NStevenU/WaveCanvas/include/logo_data.h

#pragma once
#include <Arduino.h>

// Icon: logo (logo.gif, 3143 bytes)
const size_t ICON_LOGO_GIF_SIZE = 3143;
const uint8_t ICON_LOGO_GIF_DATA[] PROGMEM = {
0x47, 0x49, 0x46, 0x38, 0x39, 0x61, 0xb6, 0x00, 0x2a, 0x00, 0x87, 0x00, 0x00, 0xf0, 0xf0, 0xf0, 
0xef, 0xef, 0xef, 0xee, 0xee, 0xee, 0xed, 0xed, 0xed, 0xec, 0xec, 0xec, 0xeb, 0xeb, 0xeb, 0xea, 
0xea, 0xea, 0xe9, 0xe9, 0xe9, 0xe8, 0xe8, 0xe8, 0xe7, 0xe7, 0xe7, 0xe6, 0xe6, 0xe6, 0xe5, 0xe5, 
0xe5, 0xe4, 0xe4, 0xe4, 0xe3, 0xe3, 0xe3, 0xe2, 0xe2, 0xe2, 0xe1, 0xe1, 0xe1, 0xe0, 0xe0, 0xe0, 
0xdf, 0xdf, 0xdf, 0xde, 0xde, 0xde, 0xdc, 0xdc, 0xdc, 0xdb, 0xdb, 0xdb, 0xda, 0xda, 0xda, 0xd9, 
0xd9, 0xd9, 0xd8, 0xd8, 0xd8, 0xd7, 0xd7, 0xd7, 0xd6, 0xd6, 0xd6, 0xd5, 0xd5, 0xd5, 0xd4, 0xd4, 
0xd4, 0xd3, 0xd3, 0xd3, 0xd2, 0xd2, 0xd2, 0xd1, 0xd1, 0xd1, 0xd0, 0xd0, 0xd0, 0xcf, 0xcf, 0xcf, 
0xce, 0xce, 0xce, 0xcd, 0xcd, 0xcd, 0xcc, 0xcc, 0xcc, 0xcb, 0xcb, 0xcb, 0xca, 0xca, 0xca, 0xc8, 
0xc8, 0xc8, 0xc7, 0xc7, 0xc7, 0xc6, 0xc6, 0xc6, 0xc4, 0xc4, 0xc4, 0xc3, 0xc3, 0xc3, 0xc2, 0xc2, 
0xc2, 0xc1, 0xc1, 0xc1, 0xc0, 0xc0, 0xc0, 0xbf, 0xbf, 0xbf, 0xbe, 0xbe, 0xbe, 0xbc, 0xbc, 0xbc, 
0xbb, 0xbb, 0xbb, 0xb9, 0xb9, 0xb9, 0xb8, 0xb8, 0xb8, 0xb7, 0xb7, 0xb7, 0xb6, 0xb6, 0xb6, 0xb5, 
0xb5, 0xb5, 0xb4, 0xb4, 0xb4, 0xb3, 0xb3, 0xb3, 0xb2, 0xb2, 0xb2, 0xb1, 0xb1, 0xb1, 0xb0, 0xb0, 
0xb0, 0xaf, 0xaf, 0xaf, 0xad, 0xad, 0xad, 0xac, 0xac, 0xac, 0xab, 0xab, 0xab, 0xaa, 0xaa, 0xaa, 
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
0x25, 0x25, 0x25, 0x24, 0x24, 0x24, 0x23, 0x23, 0x23, 0x22, 0x22, 0x22, 0x21, 0x21, 0x21, 0x20, 
0x20, 0x20, 0x1f, 0x1f, 0x1f, 0x1e, 0x1e, 0x1e, 0x1d, 0x1d, 0x1d, 0x1c, 0x1c, 0x1c, 0x1b, 0x1b, 
0x1b, 0x1a, 0x1a, 0x1a, 0x19, 0x19, 0x19, 0x18, 0x18, 0x18, 0x17, 0x17, 0x17, 0x16, 0x16, 0x16, 
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
};
