NStevenU/WaveCanvas/include/icon_data.h

#pragma once
#include <Arduino.h>

// Icon: music (music.gif, 136 bytes)
const size_t ICON_MUSIC_GIF_SIZE = 136;
const uint8_t ICON_MUSIC_GIF_DATA[] PROGMEM = {
0x47, 0x49, 0x46, 0x38, 0x39, 0x61, 0x10, 0x00, 0x10, 0x00, 0x82, 0x00, 0x00, 0xcc, 0xcc, 0xcc, 
0x99, 0x99, 0x99, 0x66, 0x66, 0x66, 0x33, 0x33, 0x33, 0x00, 0x00, 0x00, 0x00, 0x00, 0x00, 0x00, 
0x00, 0x00, 0x00, 0x00, 0x00, 0x21, 0xf9, 0x04, 0x09, 0x00, 0x00, 0x05, 0x00, 0x2c, 0x00, 0x00, 
0x00, 0x00, 0x10, 0x00, 0x10, 0x00, 0x40, 0x08, 0x4d, 0x00, 0x0b, 0x08, 0x1c, 0x48, 0xb0, 0xa0, 
0xc1, 0x81, 0x04, 0x02, 0x10, 0x38, 0x68, 0x30, 0xe1, 0x42, 0x02, 0x0b, 0x11, 0x02, 0x10, 0x40, 
0x91, 0xe2, 0x80, 0x88, 0x0c, 0x11, 0x06, 0x10, 0x80, 0x31, 0xa3, 0x43, 0x86, 0x04, 0x00, 0x88, 
0x9c, 0x78, 0x11, 0x24, 0xc4, 0x93, 0x19, 0x1b, 0x42, 0x4c, 0xa9, 0x11, 0x65, 0xca, 0x8f, 0x2c, 
0x0b, 0xc0, 0x3c, 0x78, 0x32, 0x24, 0x47, 0x9a, 0x13, 0x2b, 0x0a, 0x28, 0xd9, 0x70, 0xe7, 0x80, 
0x9f, 0x3c, 0x63, 0x32, 0x0c, 0x08, 0x00, 0x3b, 
};

// Icon: piano (piano.gif, 151 bytes)
const size_t ICON_PIANO_GIF_SIZE = 151;
const uint8_t ICON_PIANO_GIF_DATA[] PROGMEM = {
0x47, 0x49, 0x46, 0x38, 0x39, 0x61, 0x10, 0x00, 0x10, 0x00, 0x82, 0x00, 0x00, 0xff, 0xff, 0xff, 
0xcc, 0xcc, 0xcc, 0x1b, 0xb0, 0x1b, 0x66, 0x66, 0x66, 0x33, 0x33, 0x33, 0x00, 0x33, 0x00, 0x00, 
0x00, 0x00, 0x00, 0x00, 0x00, 0x21, 0xf9, 0x04, 0x09, 0x00, 0x00, 0x07, 0x00, 0x2c, 0x00, 0x00, 
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
0x04, 0xa9, 0x90, 0x22, 0xc7, 0x03, 0x06, 0x52, 0x9e, 0x74, 0x38, 0xa0, 0xa5, 0x49, 0x83, 0x08, 
0x01, 0x78, 0x7c, 0x39, 0x30, 0xe6, 0xcc, 0x86, 0x36, 0x25, 0xd2, 0xac, 0x79, 0x93, 0xe3, 0xc5, 
0x8c, 0x1b, 0x4f, 0xfe, 0xd4, 0xb8, 0x72, 0x65, 0x40, 0x00, 0x3b, 
};
