NStevenU/WaveCanvas/include/tetris_midi_data.h

#pragma once

#include <Arduino.h>

// Tetris Korobeiniki 2/3 Balanced 3D Symphony MIDI Data (8547 bytes)
#define TETRIS_KOROBEINIKI_MIDI_SIZE 8547

const uint8_t TETRIS_KOROBEINIKI_MIDI[] PROGMEM = {
    0x4D, 0x54, 0x68, 0x64, 0x00, 0x00, 0x00, 0x06, 0x00, 0x01, 0x00, 0x03, 0x01, 0x80, 0x4D, 0x54,
    0x72, 0x6B, 0x00, 0x00, 0x00, 0x13, 0x00, 0xFF, 0x58, 0x04, 0x04, 0x02, 0x18, 0x08, 0x00, 0xFF,
    0x51, 0x03, 0x08, 0x2C, 0xA2, 0x00, 0xFF, 0x2F, 0x00, 0x4D, 0x54, 0x72, 0x6B, 0x00, 0x00, 0x11,
    0x67, 0x00, 0xC0, 0x5A, 0x00, 0xB0, 0x07, 0x5A, 0x00, 0xB0, 0x0B, 0x7F, 0x00, 0xB0, 0x0A, 0x40,
    0x00, 0xB0, 0x5B, 0x3C, 0x00, 0xB0, 0x5D, 0x23, 0x00, 0xC7, 0x09, 0x00, 0xB7, 0x07, 0x55, 0x00,
    0xB7, 0x0B, 0x7F, 0x00, 0xB7, 0x0A, 0x4B, 0x00, 0xB7, 0x5B, 0x46, 0x00, 0xB7, 0x5D, 0x2D, 0x00,
    0xC2, 0x5A, 0x00, 0xB2, 0x07, 0x50, 0x00, 0xB2, 0x0B, 0x7F, 0x00, 0xB2, 0x0A, 0x1E, 0x00, 0xB2,
    0x5B, 0x4B, 0x00, 0xB2, 0x5D, 0x32, 0x00, 0xC5, 0x30, 0x00, 0xB5, 0x07, 0x50, 0x00, 0xB5, 0x0B,
    0x7F, 0x00, 0xB5, 0x0A, 0x14, 0x00, 0xB5, 0x5B, 0x55, 0x00, 0xB5, 0x5D, 0x46, 0x00, 0xC6, 0x31,
    0x00, 0xB6, 0x07, 0x50, 0x00, 0xB6, 0x0B, 0x7F, 0x00, 0xB6, 0x0A, 0x6C, 0x00, 0xB6, 0x5B, 0x55,
    0x00, 0xB6, 0x5D, 0x46, 0x00, 0xCA, 0x3D, 0x00, 0xBA, 0x07, 0x55, 0x00, 0xBA, 0x0B, 0x7F, 0x00,
    0xBA, 0x0A, 0x58, 0x00, 0xBA, 0x5B, 0x50, 0x00, 0xBA, 0x5D, 0x32, 0x00, 0x90, 0x40, 0x52, 0x00,
    0x97, 0x4C, 0x3E, 0x00, 0x9A, 0x34, 0x44, 0x00, 0x92, 0x3B, 0x3A, 0x00, 0x95, 0x3B, 0x38, 0x00,
    0x96, 0x47, 0x36, 0x81, 0x40, 0x82, 0x3B, 0x00, 0x00, 0x85, 0x3B, 0x00, 0x00, 0x86, 0x47, 0x00,
    0x60, 0x80, 0x40, 0x00, 0x00, 0x87, 0x4C, 0x00, 0x00, 0x8A, 0x34, 0x00, 0x00, 0x90, 0x3B, 0x52,
    0x00, 0x97, 0x47, 0x3E, 0x00, 0x9A, 0x2F, 0x44, 0x00, 0x92, 0x38, 0x3A, 0x00, 0x95, 0x38, 0x38,
    0x00, 0x96, 0x44, 0x36, 0x81, 0x10, 0x80, 0x3B, 0x00, 0x00, 0x87, 0x47, 0x00, 0x00, 0x8A, 0x2F,
    0x00, 0x00, 0x82, 0x38, 0x00, 0x00, 0x85, 0x38, 0x00, 0x00, 0x86, 0x44, 0x00, 0x00, 0x90, 0x3C,
    0x52, 0x00, 0x97, 0x48, 0x3E, 0x00, 0x9A, 0x30, 0x44, 0x00, 0x92, 0x39, 0x3A, 0x00, 0x95, 0x39,
    0x38, 0x00, 0x96, 0x45, 0x36, 0x81, 0x10, 0x80, 0x3C, 0x00, 0x00, 0x87, 0x48, 0x00, 0x00, 0x8A,
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
